takeokas/takepCosmac/kicad_files/cpu.kicad_sch

## KiCad design kicad_files/cpu.kicad_sch (2026-08-15)

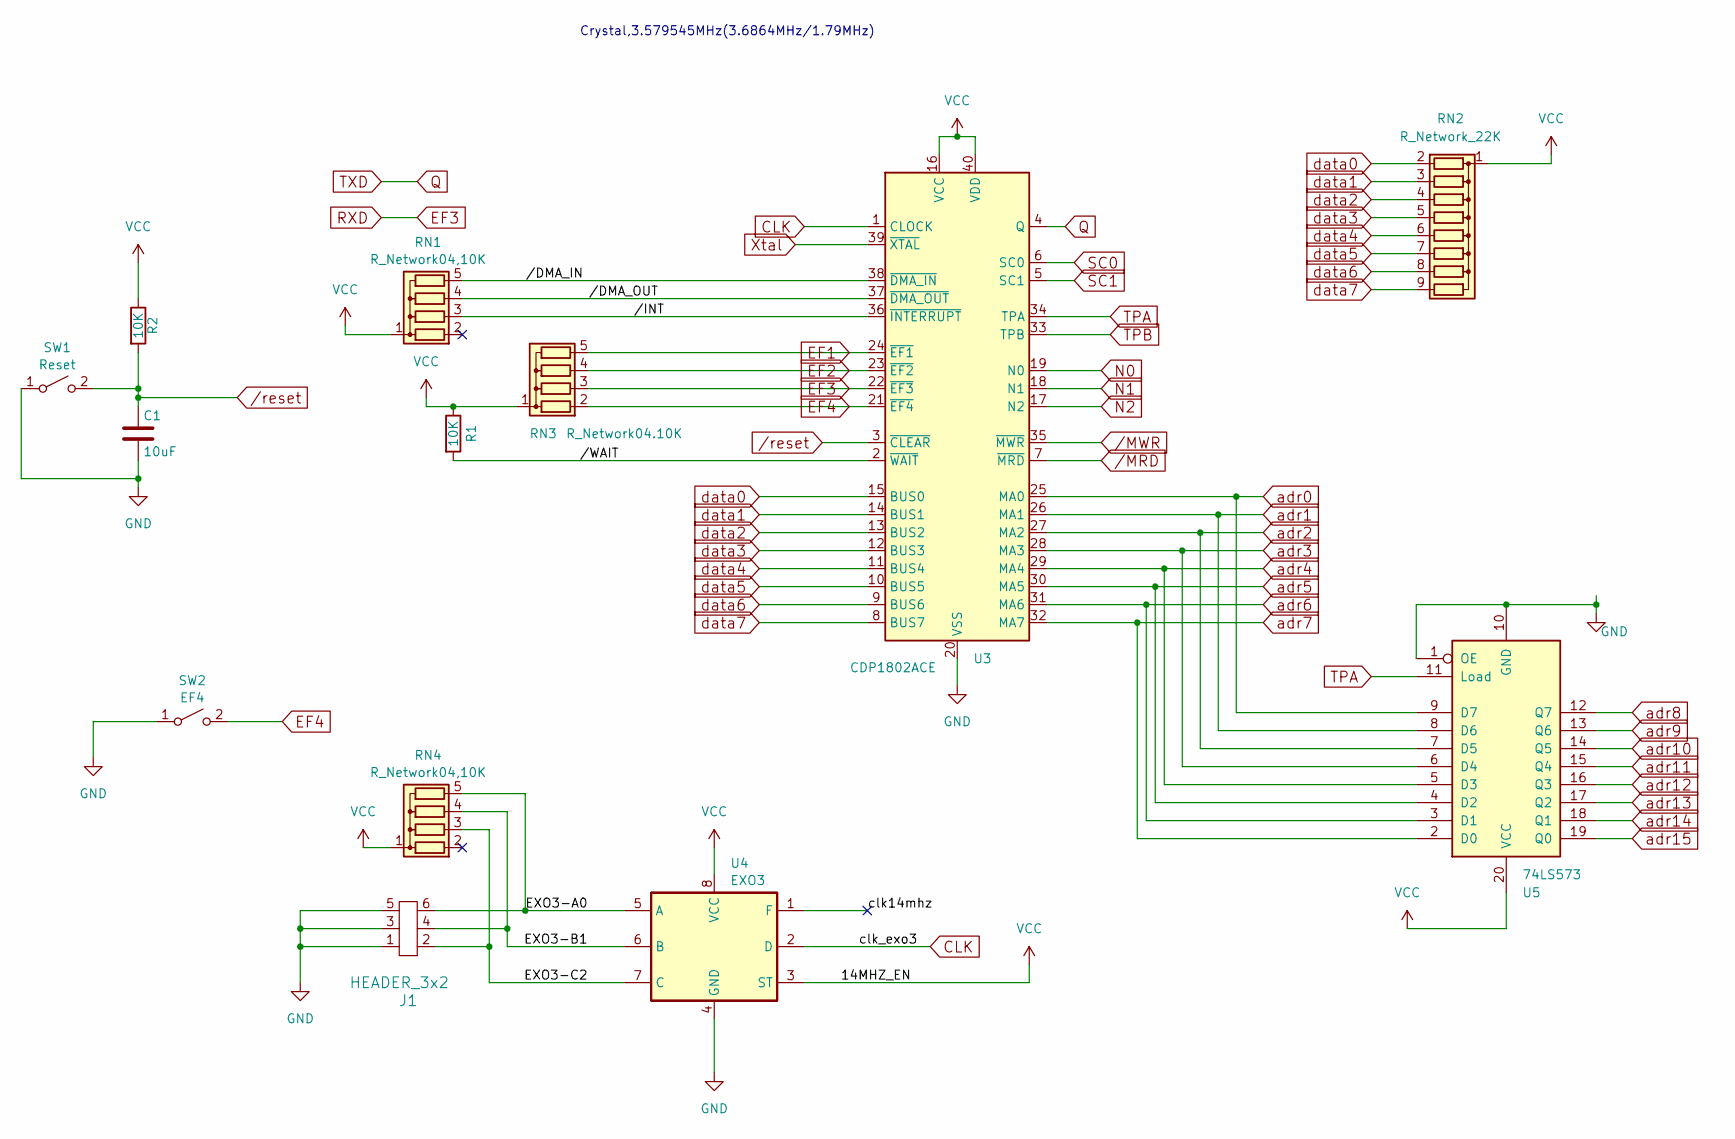
[picture p18: schematic cpu.kicad_sch]

Parts:
C1: 10uF; C_Disc_D3.0mm_W2.0mm_P2.50mm
J1: HEADER_3x2; PinHeader_2x03_P2.54mm_Vertical
R1: 10K; R_Axial_DIN0207_L6.3mm_D2.5mm_P7.62mm_Horizontal
R2: 10K; R_Axial_DIN0207_L6.3mm_D2.5mm_P2.54mm_Vertical
RN1, RN4: R_Network04,10K; R_Array_SIP5
RN2: R_Network_22K; R_Array_SIP9
RN3: R_Network04.10K; R_Array_SIP5
SW1: Reset; SW_PUSH_1P1T_6x3.5mm_H5.0_APEM_MJTP1250
SW2: EF4; SW_PUSH_1P1T_6x3.5mm_H5.0_APEM_MJTP1250
U3: CDP1802ACE; DIP-40_W15.24mm_Socket
U4: EXO3; DIP-8_W7.62mm
U5: 74LS573; DIP-20_W7.62mm

Connections:
/reset: C1.1, R2.2, SW1.2 (B)
CLK: U3.1 (CLOCK), U4.2 (D)
EF1: RN3.5 (R4), U3.24 (~EF1)
EF2: RN3.4 (R3), U3.23 (~EF2)
EF3: RN3.3 (R2), U3.22 (~EF3)
EF4: RN3.2 (R1), SW2.2 (B), U3.21 (~EF4)
EXO3-A0: J1.6, RN4.5 (R4), U4.5 (A)
EXO3-B1: J1.4, RN4.4 (R3), U4.6 (B)
EXO3-C2: J1.2, RN4.3 (R2), U4.7 (C)
GND: C1.2, J1.1, J1.3, J1.5, SW1.1 (A), SW2.1 (A), U3.20 (VSS), U4.4 (GND), U5.1 (OE), U5.10 (GND)
N0: U3.19 (N0)
N1: U3.18 (N1)
N2: U3.17 (N2)
Q: U3.4 (Q)
SC0: U3.6 (SC0)
SC1: U3.5 (SC1)
TPA: U3.34 (TPA), U5.11 (Load)
TPB: U3.33 (TPB)
VCC: R1.1, R2.1, RN1.1 (common), RN2.1 (common), RN3.1 (common), RN4.1 (common), U3.16 (VCC), U3.40 (VDD), U4.3 (ST), U4.8 (VCC), U5.20 (VCC)
Xtal: U3.39 (~XTAL)
adr0: U3.25 (MA0), U5.9 (D7)
adr1: U3.26 (MA1), U5.8 (D6)
adr2: U3.27 (MA2), U5.7 (D5)
adr3: U3.28 (MA3), U5.6 (D4)
adr4: U3.29 (MA4), U5.5 (D3)
adr5: U3.30 (MA5), U5.4 (D2)
adr6: U3.31 (MA6), U5.3 (D1)
adr7: U3.32 (MA7), U5.2 (D0)
adr8: U5.12 (Q7)
adr9: U5.13 (Q6)
adr10: U5.14 (Q5)
adr11: U5.15 (Q4)
adr12: U5.16 (Q3)
adr13: U5.17 (Q2)
adr14: U5.18 (Q1)
adr15: U5.19 (Q0)
clk14mhz: U4.1 (F)
data0: RN2.2 (R1), U3.15 (BUS0)
data1: RN2.3 (R2), U3.14 (BUS1)
data2: RN2.4 (R3), U3.13 (BUS2)
data3: RN2.5 (R4), U3.12 (BUS3)
data4: RN2.6 (R5), U3.11 (BUS4)
data5: RN2.7 (R6), U3.10 (BUS5)
data6: RN2.8 (R7), U3.9 (BUS6)
data7: RN2.9 (R8), U3.8 (BUS7)
/DMA_IN: RN1.5 (R4), U3.38 (~DMA_IN)
/DMA_OUT: RN1.4 (R3), U3.37 (~DMA_OUT)
/INT: RN1.3 (R2), U3.36 (~INTERRUPT)
/MRD: U3.7 (~MRD)
/MWR: U3.35 (~MWR)
/WAIT: R1.2, U3.2 (~WAIT)
/reset: U3.3 (~CLEAR)

Notes on the sheet:
Crystal,3.579545MHz(3.6864MHz/1.79MHz)
