takeokas/takepCosmac/kicad_files/dummy.kicad_sch

## KiCad design kicad_files/dummy.kicad_sch (2026-08-15)

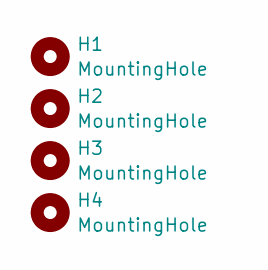
[picture p19: schematic dummy.kicad_sch]

Parts:
H1, H2, H3, H4: MountingHole; MountingHole_3.2mm_M3
