takeokas/takepCosmac/kicad_files/led.kicad_sch

## KiCad design kicad_files/led.kicad_sch (2026-08-15)

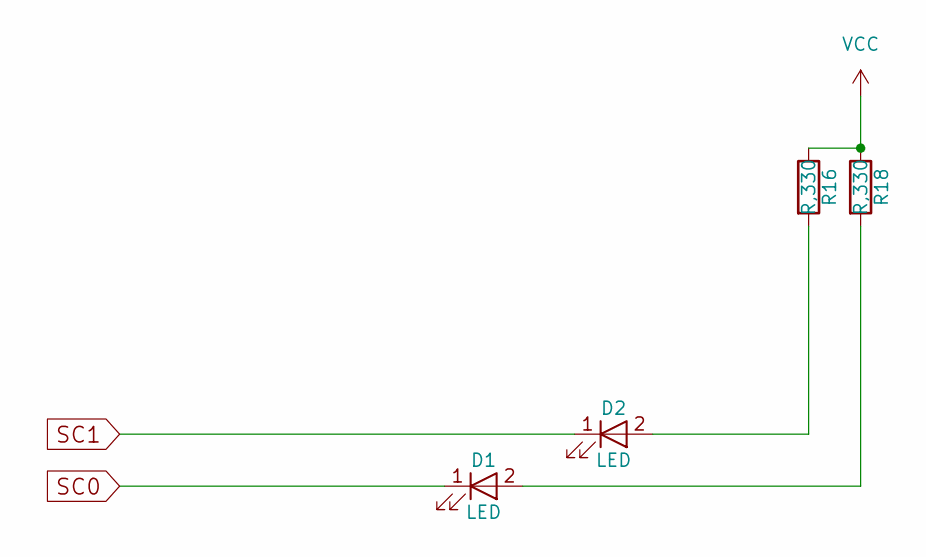
[picture p20: schematic led.kicad_sch]

Parts:
D1, D2: LED; LED_D1.8mm_W3.3mm_H2.4mm
R16, R18: R,330; R_Axial_DIN0207_L6.3mm_D2.5mm_P2.54mm_Vertical

Connections:
unnamed: D1.2 (A), R18.2
unnamed: D2.2 (A), R16.2
SC0: D1.1 (K)
SC1: D2.1 (K)
VCC: R16.1, R18.1
