takeokas/takepCosmac/kicad_files/mem.kicad_sch

## KiCad design kicad_files/mem.kicad_sch (2026-08-15)

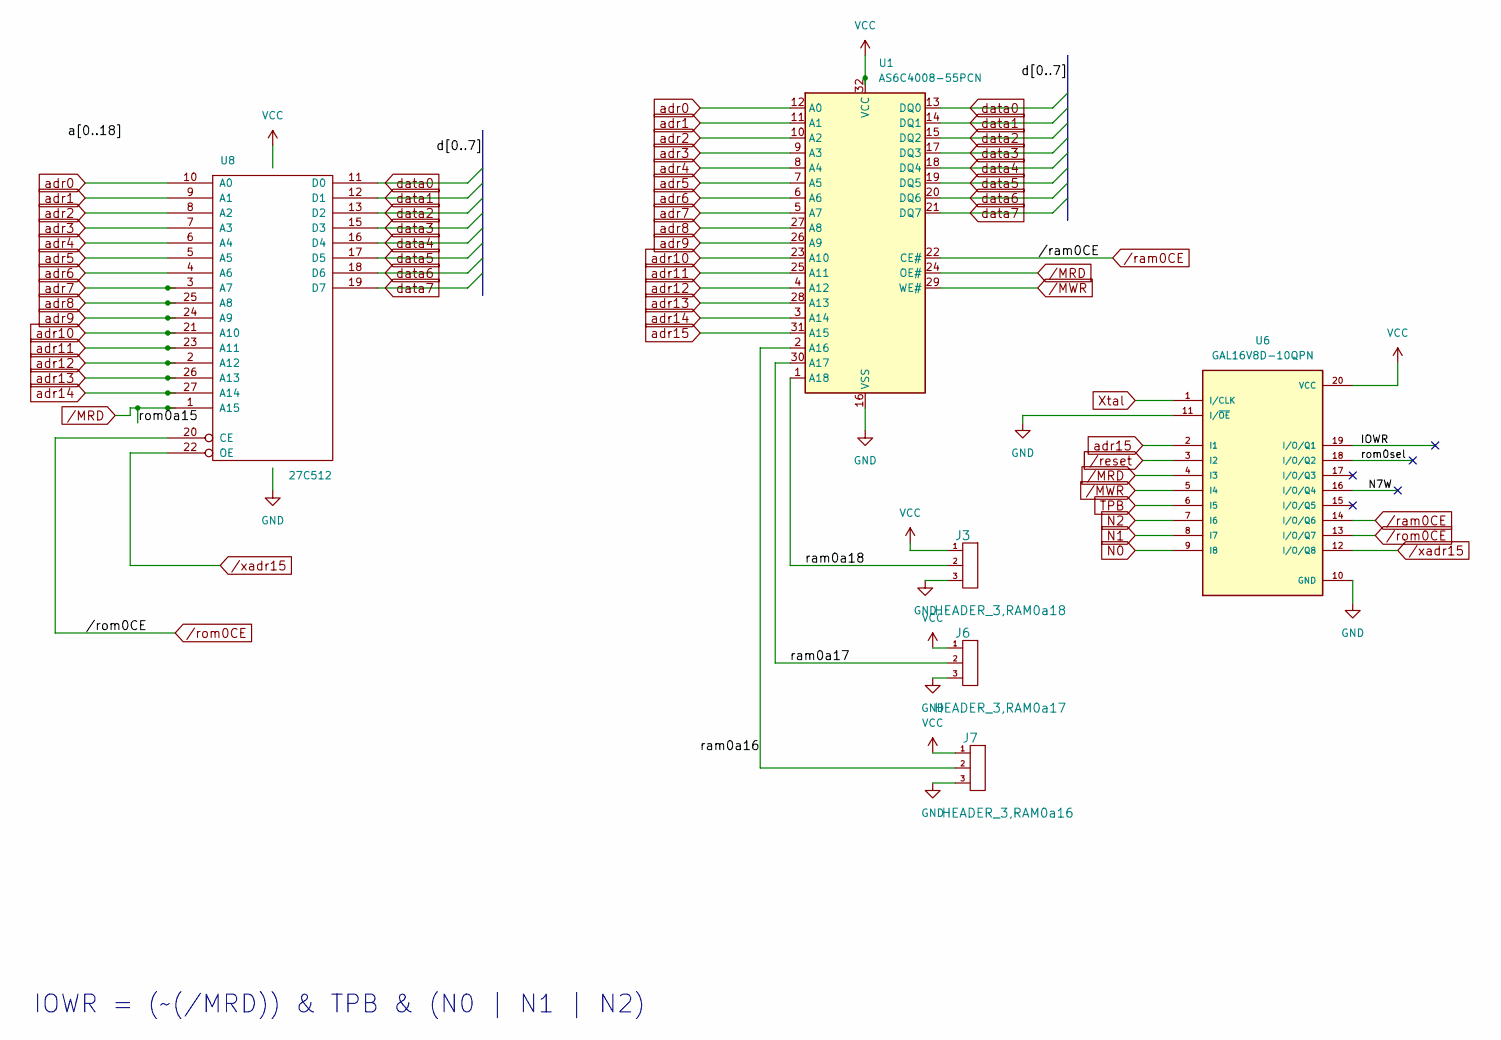
[picture p21: schematic mem.kicad_sch]

Parts:
J3: HEADER_3,RAM0a18; PinHeader_1x03_P2.54mm_Vertical
J6: HEADER_3,RAM0a17; PinHeader_1x03_P2.54mm_Vertical
J7: HEADER_3,RAM0a16; PinHeader_1x03_P2.54mm_Vertical
U1: AS6C4008-55PCN; DIP-32_W15.24mm
U6: GAL16V8D-10QPN; DIP-20_W7.62mm_Socket; PARTREV 16v8_11
U8: 27C512; DIP-28_W15.24mm_Socket

Connections:
GND: J3.3, J6.3, J7.3, U1.16 (VSS), U6.10 (GND), U6.11 (I/~OE), U8.14 (GND)
IOWR: U6.19 (I/O/Q1)
N0: U6.9 (I8)
N1: U6.8 (I7)
N2: U6.7 (I6)
N7W: U6.16 (I/O/Q4)
TPB: U6.6 (I5)
VCC: J3.1, J6.1, J7.1, U1.32 (VCC), U6.20 (VCC), U8.28 (VCC)
Xtal: U6.1 (I/CLK)
adr0: U1.12 (A0), U8.10 (A0)
adr1: U1.11 (A1), U8.9 (A1)
adr2: U1.10 (A2), U8.8 (A2)
adr3: U1.9 (A3), U8.7 (A3)
adr4: U1.8 (A4), U8.6 (A4)
adr5: U1.7 (A5), U8.5 (A5)
adr6: U1.6 (A6), U8.4 (A6)
adr7: U1.5 (A7), U8.3 (A7)
adr8: U1.27 (A8), U8.25 (A8)
adr9: U1.26 (A9), U8.24 (A9)
adr10: U1.23 (A10), U8.21 (A10)
adr11: U1.25 (A11), U8.23 (A11)
adr12: U1.4 (A12), U8.2 (A12)
adr13: U1.28 (A13), U8.26 (A13)
adr14: U1.3 (A14), U8.27 (A14)
adr15: U1.31 (A15), U6.2 (I1)
data0: U1.13 (DQ0), U8.11 (D0)
data1: U1.14 (DQ1), U8.12 (D1)
data2: U1.15 (DQ2), U8.13 (D2)
data3: U1.17 (DQ3), U8.15 (D3)
data4: U1.18 (DQ4), U8.16 (D4)
data5: U1.19 (DQ5), U8.17 (D5)
data6: U1.20 (DQ6), U8.18 (D6)
data7: U1.21 (DQ7), U8.19 (D7)
ram0a16: J7.2, U1.2 (A16)
ram0a17: J6.2, U1.30 (A17)
ram0a18: J3.2, U1.1 (A18)
rom0sel: U6.18 (I/O/Q2)
/MRD: U1.24 (OE#), U6.4 (I3), U8.1 (A15)
/MWR: U1.29 (WE#), U6.5 (I4)
/ram0CE: U1.22 (CE#), U6.14 (I/O/Q6)
/reset: U6.3 (I2)
/rom0CE: U6.13 (I/O/Q7), U8.20 (CE)
/xadr15: U6.12 (I/O/Q8), U8.22 (OE)

Notes on the sheet:
IOWR = (~(/MRD)) & TPB & (N0 | N1 | N2)
