takeokas/takepCosmac/kicad_files/takepCosmac4.kicad_sch

## KiCad design kicad_files/takepCosmac4.kicad_sch (2026-08-15)

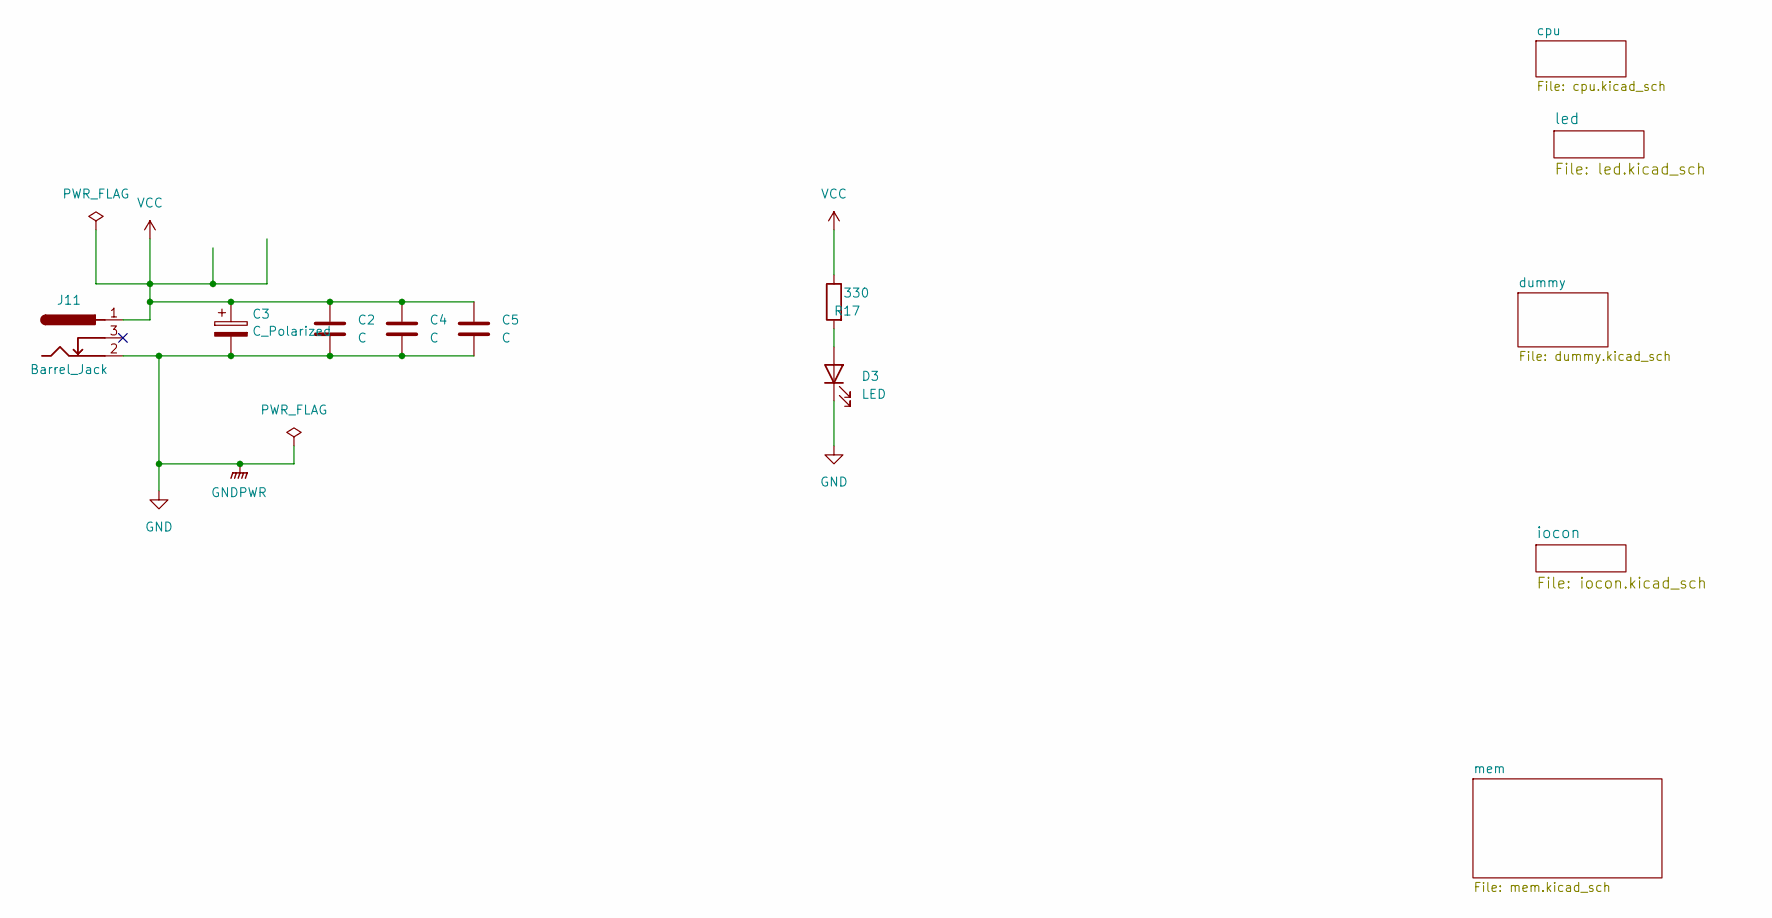
[picture p22: schematic takepCosmac4.kicad_sch]

Parts:
C2, C4, C5: C; C_Disc_D4.7mm_W2.5mm_P5.00mm
C3: C_Polarized; CP_Radial_D4.0mm_P2.00mm
D3: LED; LED_D3.0mm
J11: Barrel_Jack; BarrelJack_GCT_DCJ200-10-A_Horizontal
R17: 330; R_Axial_DIN0207_L6.3mm_D2.5mm_P2.54mm_Vertical

Connections:
GND: C2.2, C3.2, C4.2, C5.2, D3.1 (K), J11.2
unnamed: D3.2 (A), R17.2
VCC: C2.1, C3.1, C4.1, C5.1, J11.1, R17.1
